kevinshaju/TENET/3D Libraries/FS8205A--3DModel-STEP-56544.STEP

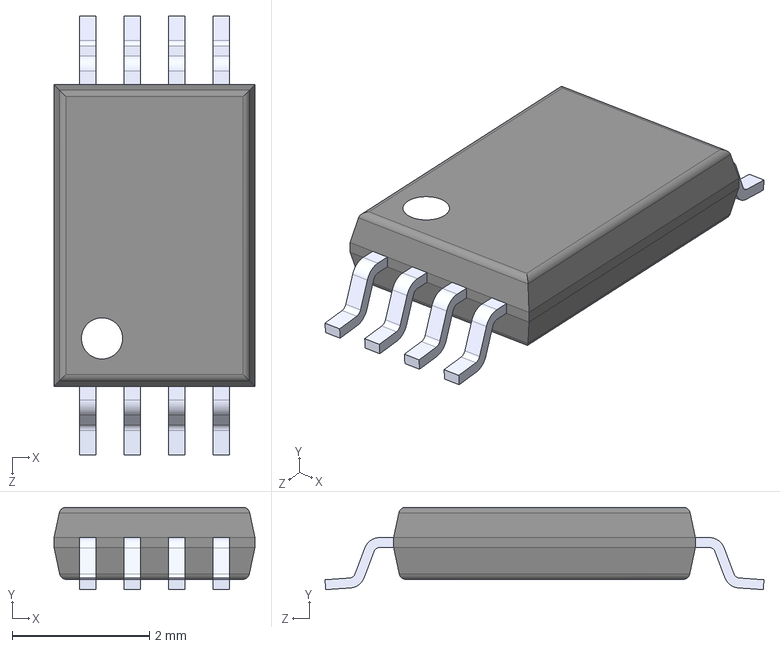
[picture p21: CAD file, 2020-09-24]
3D Libraries/FS8205A--3DModel-STEP-56544.STEP
2.93 x 1.20 x 6.40 mm
