kevinshaju/TENET/3D Libraries/TP4056-42-ESOP8.stp

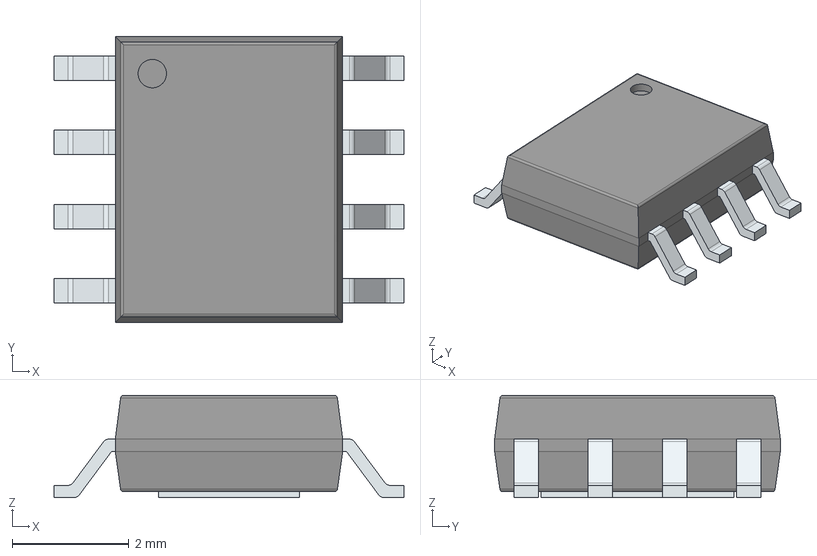
[picture p22: CAD file, 2020-09-24]
3D Libraries/TP4056-42-ESOP8.stp
6.00 x 4.90 x 1.75 mm
PinsArrayLR
ThermalPad
