kevinshaju/TENET/3D Libraries/IND_BLM18_MUR.step

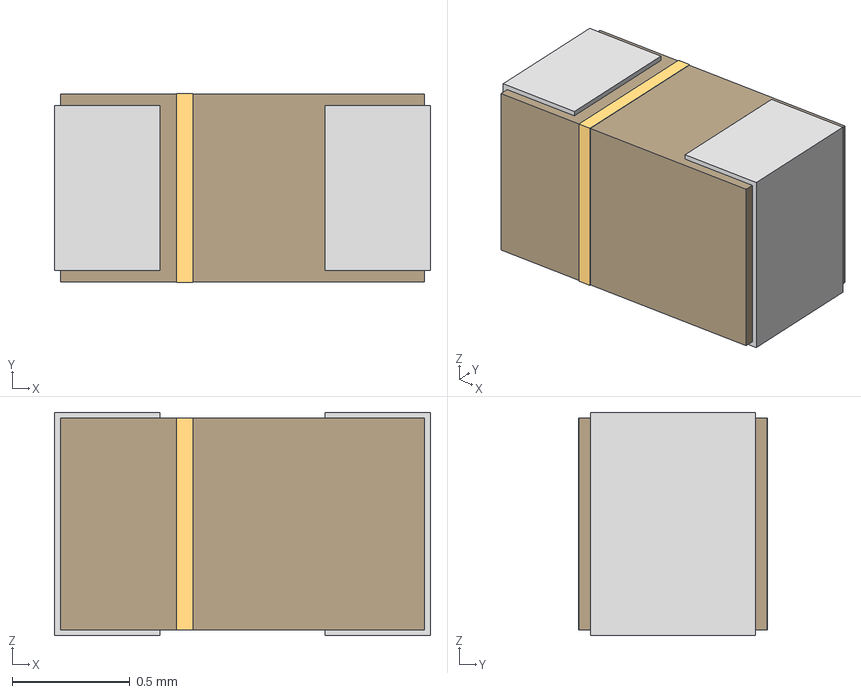
[picture p23: CAD file, 2020-09-24]
3D Libraries/IND_BLM18_MUR.step
1.60 x 0.806 x 0.95 mm
