kevinshaju/TENET/3D Libraries/c-4-1437565-2-v-3d.stp

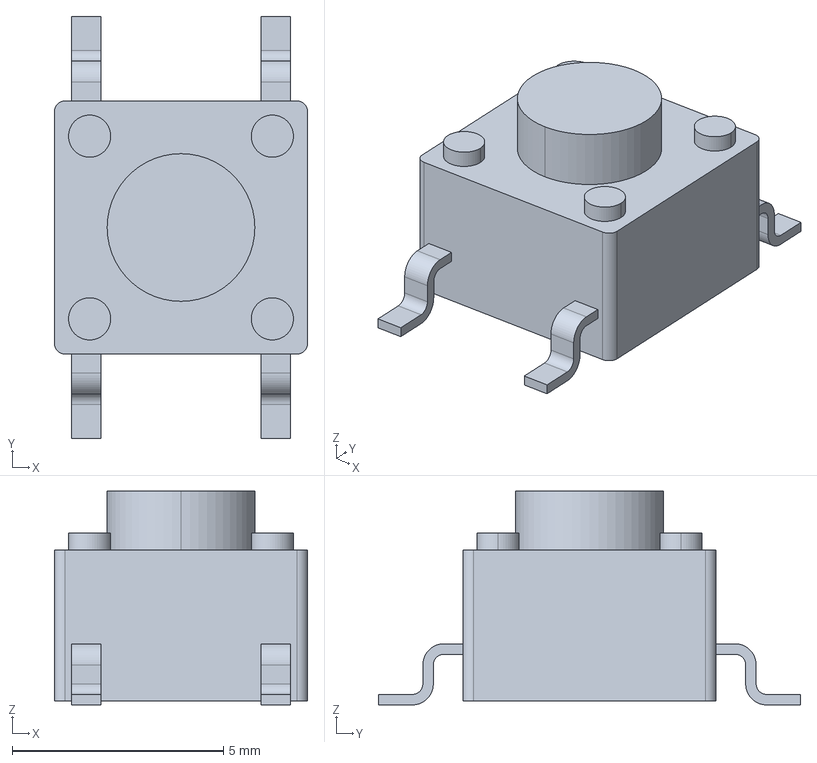
[picture p24: CAD file, 2020-09-24]
3D Libraries/c-4-1437565-2-v-3d.stp
6.00 x 10.0 x 5.07 mm
