kevinshaju/TENET/3D Libraries/TS6-SMT_H-5.0.step

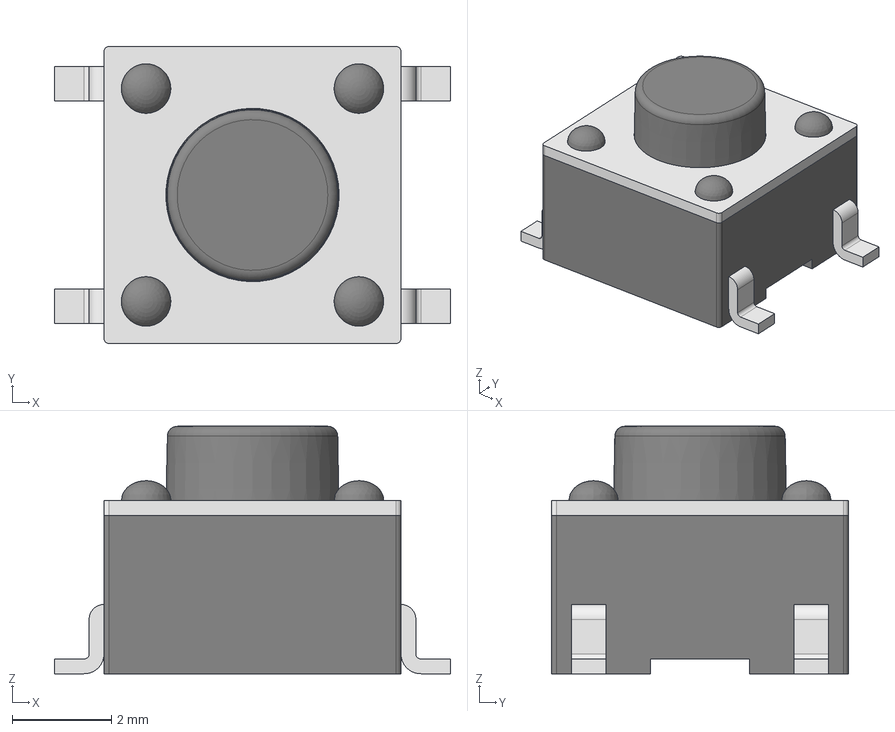
[picture p25: CAD file, 2020-09-24]
3D Libraries/TS6-SMT_H-5.0.step
8.00 x 6.00 x 5.00 mm
