kevinshaju/TENET/3D Libraries/NINA-B3x2.STEP

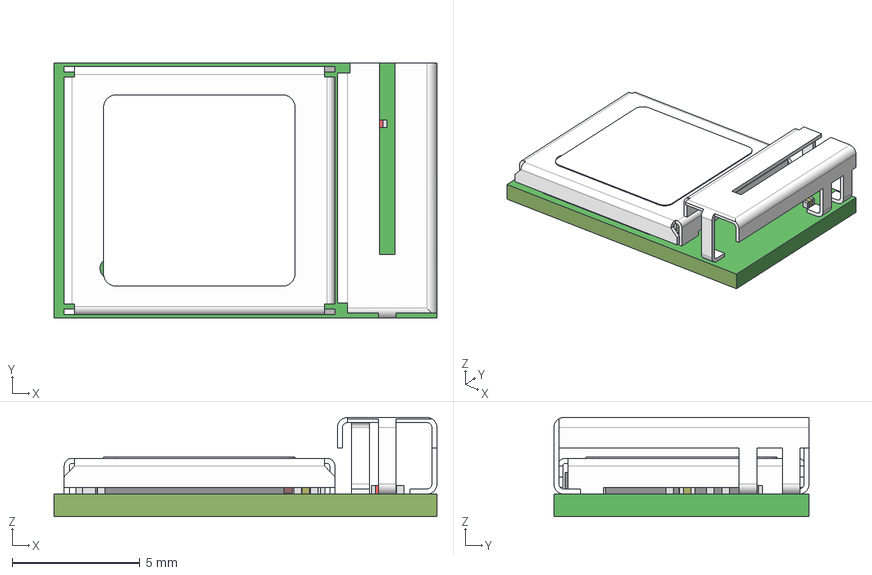
[picture p26: CAD file, 2020-09-24]
3D Libraries/NINA-B3x2.STEP
15.0 x 10.0 x 3.88 mm
PCB
X
pin-1 x 2
X2
nRF52840 7x7 mm
NINA-Bxxx Label
NINA-B3 Shieldbox
