kevinshaju/TENET/3D Libraries/PWP16_2P31X2P46_TEX-L.step

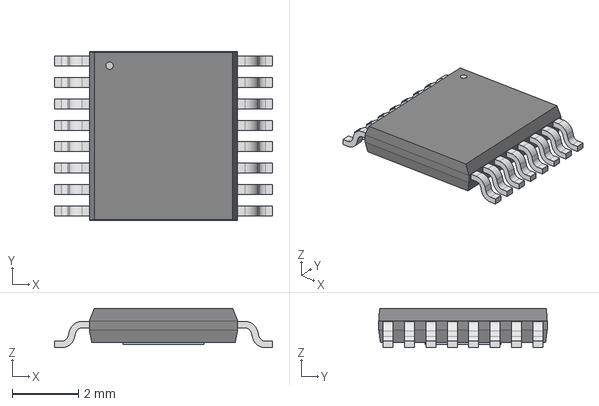
[picture p27: CAD file, 2020-09-24]
3D Libraries/PWP16_2P31X2P46_TEX-L.step
6.60 x 5.11 x 1.20 mm
