kevinshaju/TENET/3D Libraries/MPM3610.STEP

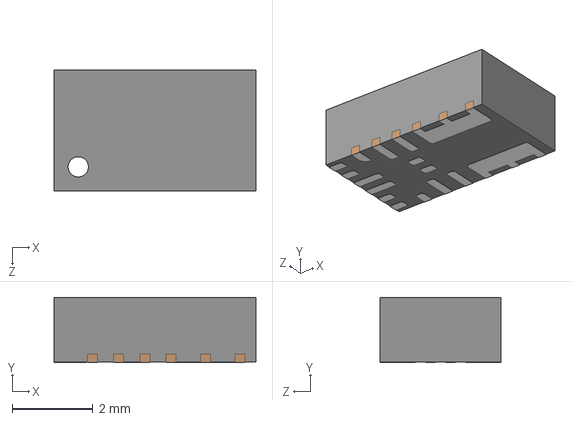
[picture p28: CAD file, 2020-09-24]
3D Libraries/MPM3610.STEP
5.00 x 1.61 x 3.00 mm
