kevinshaju/TENET/3D Libraries/Pin Header 1x15 TH Pitch 2.54mm.stp

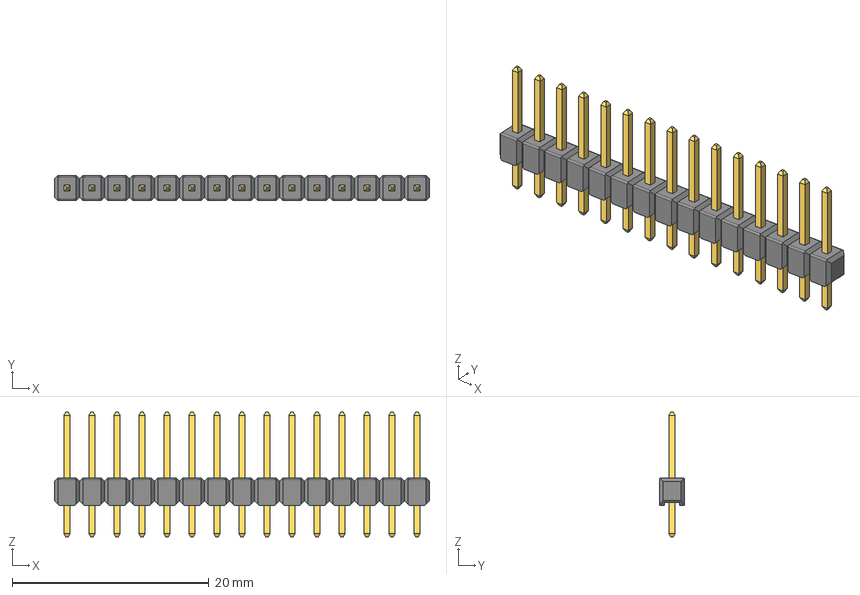
[picture p29: CAD file, 2020-09-24]
3D Libraries/Pin Header 1x15 TH Pitch 2.54mm.stp
38.1 x 2.54 x 12.7 mm
