kevinshaju/TENET/3D Libraries/QFN_DS-9930-M.step

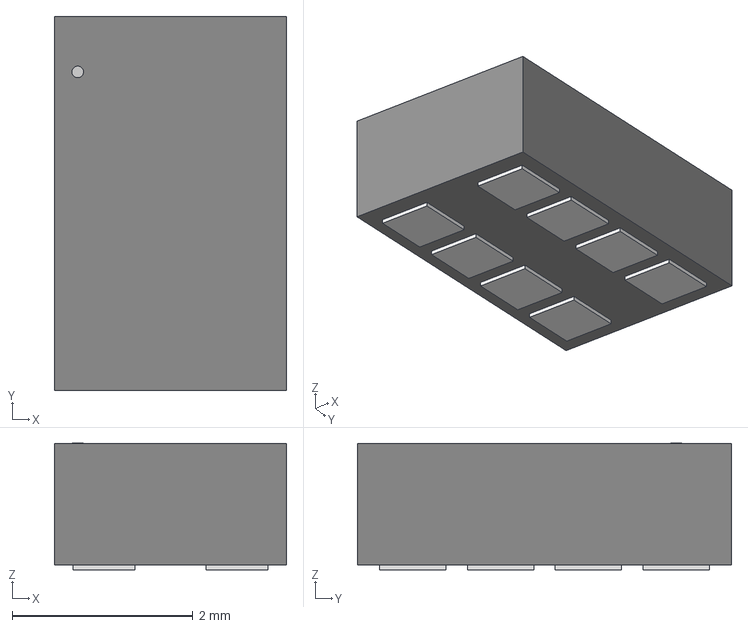
[picture p30: CAD file, 2020-09-24]
3D Libraries/QFN_DS-9930-M.step
2.57 x 4.14 x 1.40 mm
